MattisLind/teleprinterHat/src/teleprinterHat/BaudotCodec.cpp

// Letter  = 1 figures = 0

#include "BaudotCodec.h"
#include <stdio.h>

BaudotCodec::BaudotCodec(int lC) {
  letterState=-1;
  rxState=-1;
  lowerCase = lC;
}

const char BaudotCodec::lettersTable[] =  {3, 25, 14, 9, 1, 13, 26, 20, 6, 11, 15, 18, 28, 12, 24, 22, 23, 10, 5, 16, 7, 30, 19, 29, 21, 17};
const char BaudotCodec::figuresTable[] =  {22, 23, 19, 1, 10, 16, 21, 7, 6, 24};
const char BaudotCodec::rxLettersTable[] = {'\0', 'E', '\n', 'A', ' ', 'S', 'I', 'U', '\r', 'D', 'R', 'J', 'N', 'F', 'C', 'K', 'T', 'Z', 'L', 'W', 'H', 'Y', 'P', 'Q', 'O', 'B', 'G', '\0', 'M', 'X', 'V', '\0'};
const char BaudotCodec::rxFiguresTable[] = {'\0', '3', '\n', '-', ' ', '\'', '8', '7', '\r', '$', '4', '\007', ',', '!', ':', '(', '5', '+', ')', '2', '#', '6', '0', '1', '9', '?', '&', '\0', '.', '/', '=', '\0'};


char BaudotCodec::handleLetterFigure(char out, int requestedState, int * doAgain) {
  if (letterState==requestedState) {
    *doAgain = 0;
    printf("doAgain=0 |");
    return out;    
  }
  else {
    if (requestedState==1) {
      *doAgain = 1;
      letterState = 1; 
      printf("doAgain=1 letterState=1 |");
      return 31;
    }
    else {
      *doAgain = 1;
      letterState = 0;
      printf("doAgain=1 letterState=0 |");
      return 27;
    }
  }
}

char BaudotCodec::asciiToBaudot(char ch, int * doAgain) {
  int out, handled;
  if (ch >= 48 && ch <= 57) {
    // Figures
      out = figuresTable[ch-48];
      return handleLetterFigure(out, 0, doAgain); 
  } else if (ch >= 65 && ch <= 90)  { 
    out = lettersTable[ch-65]; // letters
    return handleLetterFigure(out, 1, doAgain); 
    // A-Z letters
  } else if (ch >= 97 && ch <= 122) {
    out = lettersTable[ch-97]; // letters
    return handleLetterFigure(out, 1, doAgain); 
    // a-z letter
  } else if (ch == ' ') {
    return 4;
  } else if (ch == '\r') {
    return 8;
  } else if (ch == '\n') {
    return 2;
  } else if (ch == '\0') {
    return 0;
  } else {
    handled = true;
    switch (ch) {
      case ',':
        out = 12;
        break;
      case '.':
        out = 28;       
        break;
      case ':': 
        out = 14;
        break;
      case '!': 
        out = 13;
        break;
      case '/':
        out = 29;
        break;
      case '-':
        out = 3;
        break;
      case '\'':
        out = 5;
        break;
      case '(': 
        out = 15;
        break;
      case ')':
        out = 18;
        break;
      case '&':
        out = 26;
        break;
      case '#':
        out = 20;
        break;
      case '?':
	out = 25;
	break;
       case '=':
       out = 30;
       break;
       case '+':
       out = 17;
       break;
      default:
        handled = false;
	break;
    }
    if (handled)
      return handleLetterFigure(out, 0, doAgain);
    else 
      return 0;
  }
}


int  BaudotCodec::baudotToAscii(char ch) {
  int out;
  if (rxState == -1) {
    // There are only a few charcters that unamibiously can be interpreted until we receive a LETTERS or FIGURES charcacter
    out = rxLettersTable[ch];
    switch (ch) {
      case 0:
      case 2: 
      case 4:
      case 8:
        return out;
      break;
      case 27:
        // FIGS
        rxState = 0;
        return -1;
      case 31:
        rxState = 1;
        return -1;
      default:
        return -1;
    }
  } else if (rxState == 0) {
    switch (ch) {
      case 27:
        // FIGS
        rxState = 0;
        return -1;
      case 31:
        rxState = 1;
        return -1;
      default:
	return rxFiguresTable[ch];
     }
  } else if (rxState == 1) {
    switch (ch) {
      case 27:
        // FIGS
        rxState = 0;
        return -1;
      case 31:
        rxState = 1;
        return -1;
      default:
	ch = rxLettersTable[ch];
	if (ch > 64 && ch < 98) {
	  return ch+(lowerCase<<5); 
	} else {
	  return ch;
	}
	
     }
  }
  return ch;
}
