MattisLind/teleprinterHat/src/teleprinterHat/RingBuffer.h

#define SIZE 1024

class RingBuffer {
  volatile int inPtr, outPtr, bufferFull, bufferEmpty;
  int buffer[SIZE];
public:
  int isBufferFull () {
    return bufferFull;
  };
  int isBufferEmpty () {
    return bufferEmpty;
  }
  void writeBuffer (int data);
  int readBuffer ();
  void  initBuffer ();
};
